MaibornWolff/clean-air/hardware/all_wood/pictures/frontview_open_side.png

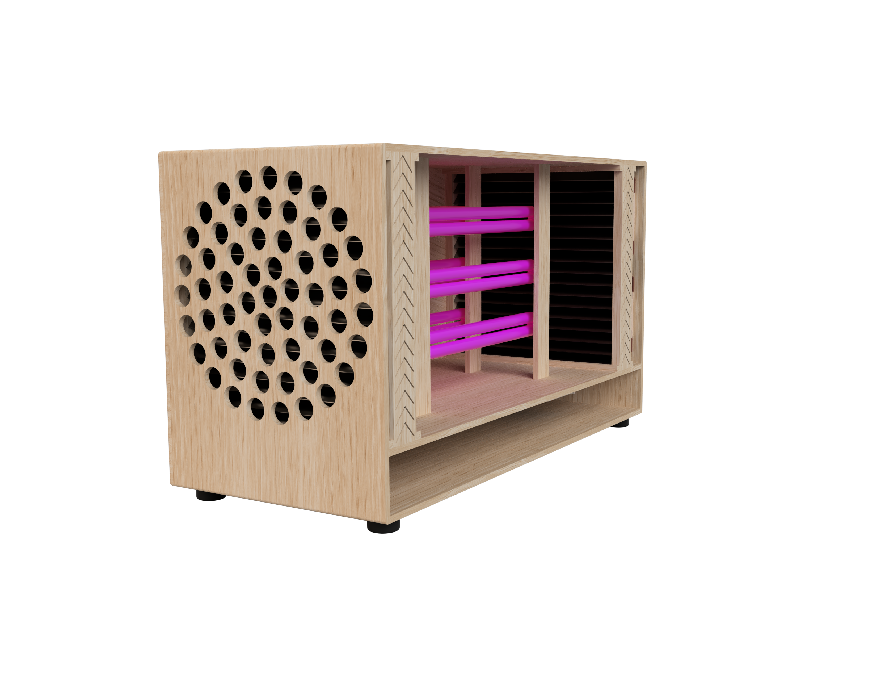
hardware/all_wood/pictures/frontview_open_side.png
