MaibornWolff/clean-air/hardware/common/uv_back_holder.stl

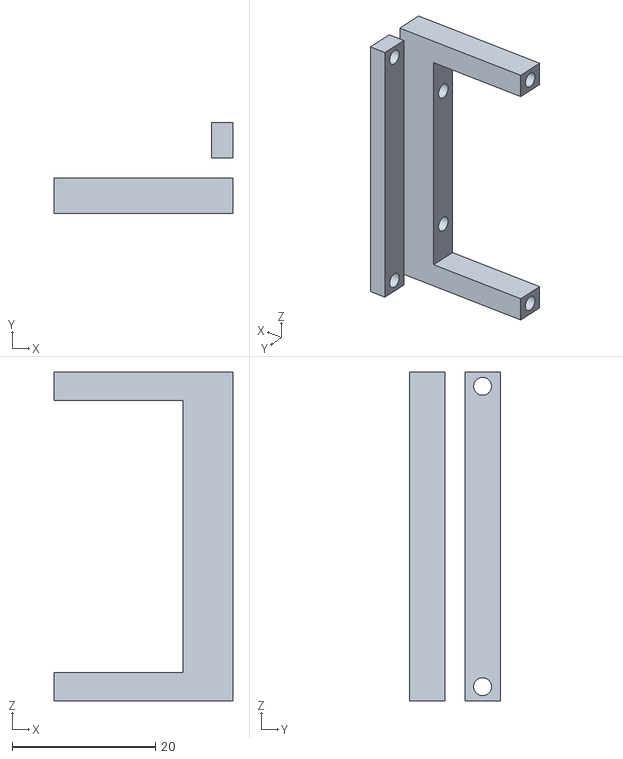
[picture p28: CAD file, 2020-12-15]
hardware/common/uv_back_holder.stl
25.0 x 12.8 x 46.0
