MaibornWolff/clean-air/hardware/all_3dprinted/universalBoxPlate_io.stl

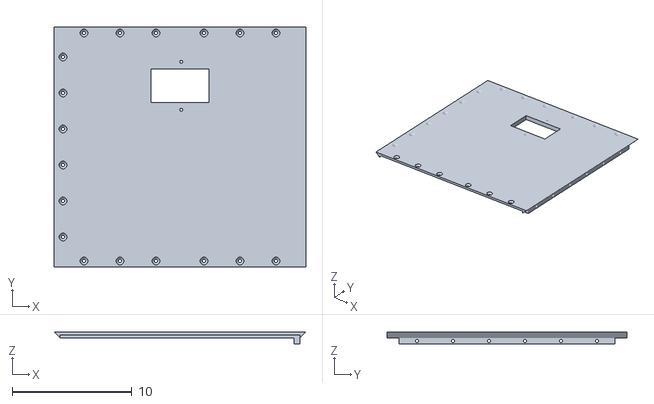
[picture p29: CAD file, 2020-11-02]
hardware/all_3dprinted/universalBoxPlate_io.stl
21.0 x 20.0 x 1.00
