MaibornWolff/clean-air/hardware/common/honeycombfront_lowprofile_fan.stl

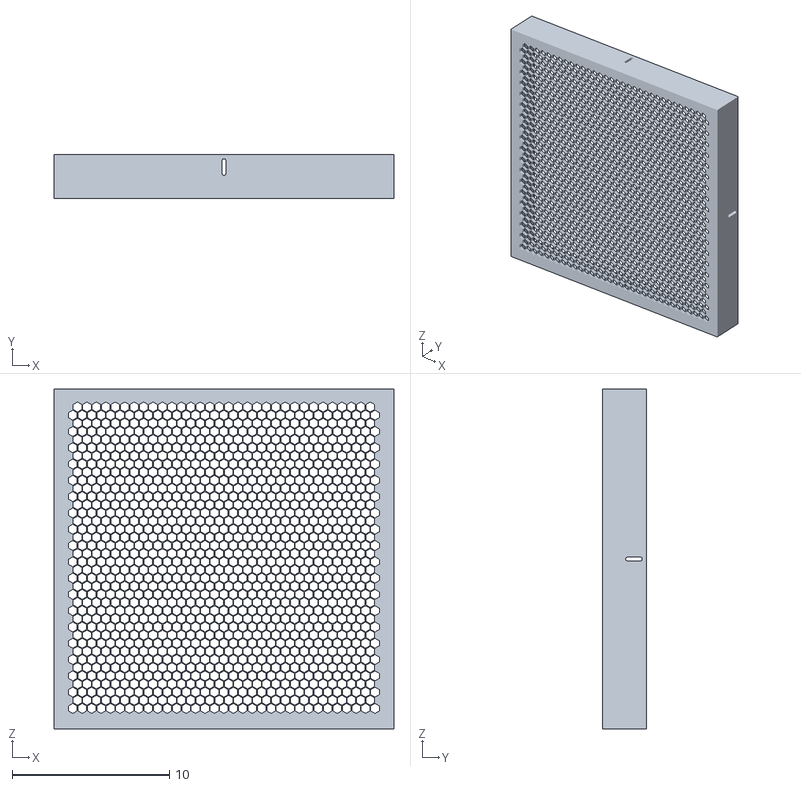
[picture p30: CAD file, 2020-11-02]
hardware/common/honeycombfront_lowprofile_fan.stl
21.6 x 2.80 x 21.6
