MaibornWolff/clean-air/documentation/images/3d_printable/inside_unfinished_1.jpg

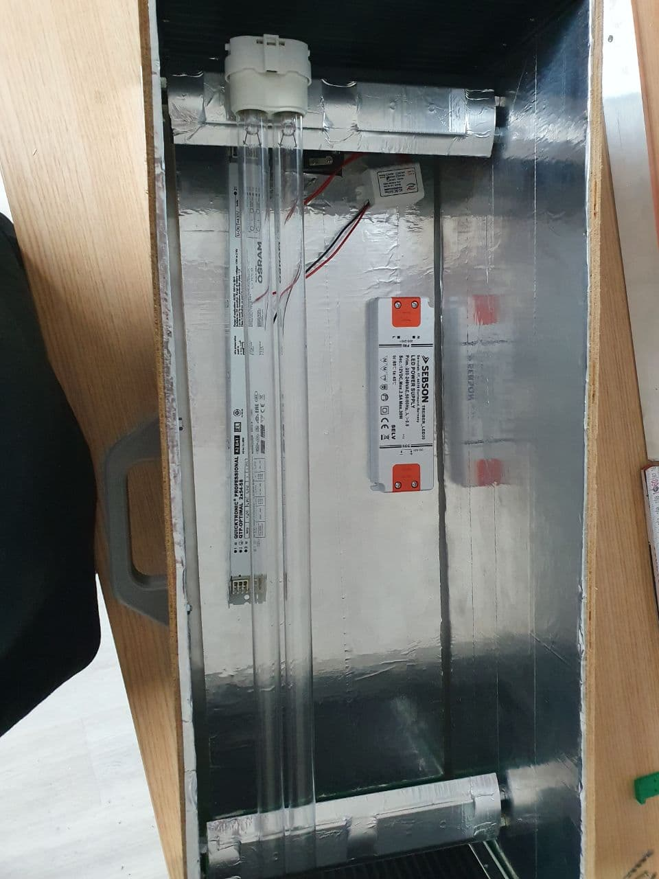
documentation/images/3d_printable/inside_unfinished_1.jpg
