MaibornWolff/clean-air/documentation/images/3d_printable/io_to_cut.jpg

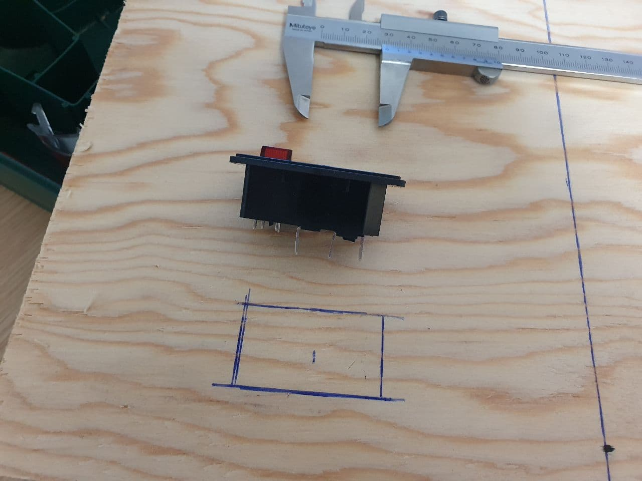
documentation/images/3d_printable/io_to_cut.jpg
