MaibornWolff/clean-air/documentation/images/3d_printable/messy_elektronics.jpg

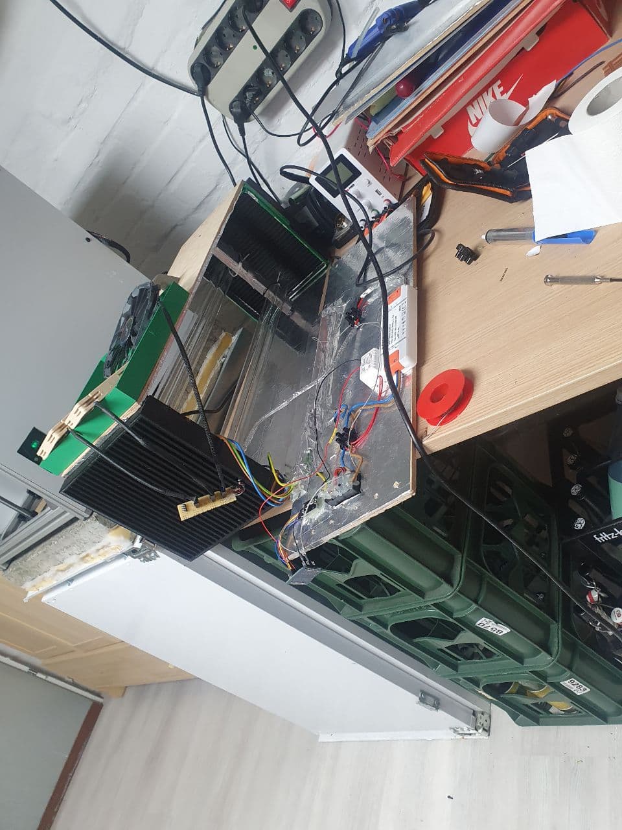
documentation/images/3d_printable/messy_elektronics.jpg
