MaibornWolff/clean-air/documentation/images/3d_printable/schable_sample.jpg

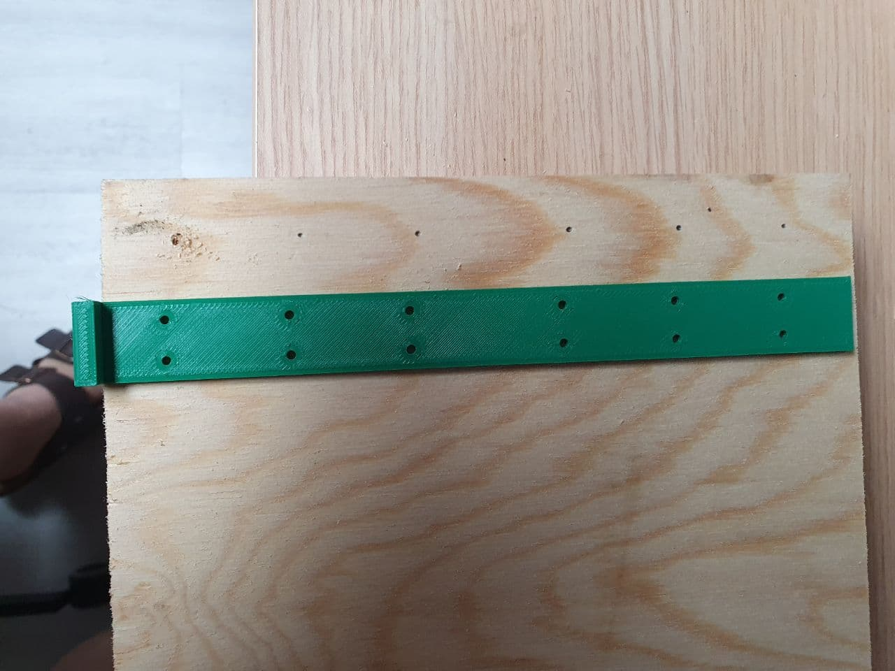
documentation/images/3d_printable/schable_sample.jpg
