MaibornWolff/clean-air/documentation/images/3d_printable/side_view.jpg

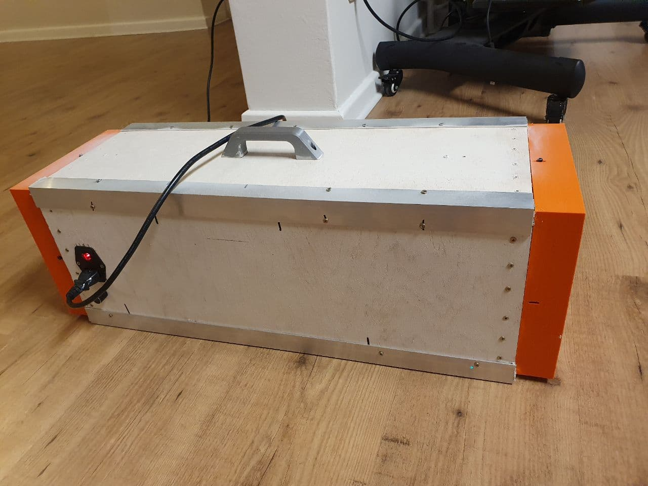
documentation/images/3d_printable/side_view.jpg
