MaibornWolff/clean-air/documentation/images/3d_printable/side_with_knob.jpg

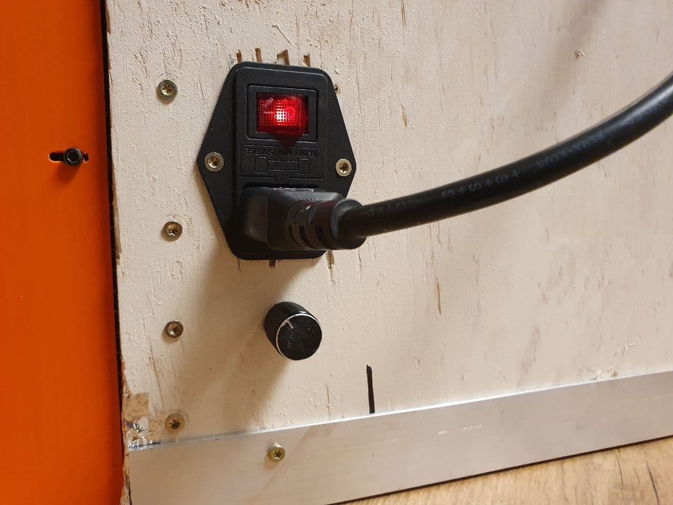
documentation/images/3d_printable/side_with_knob.jpg
