MaibornWolff/clean-air/documentation/images/3d_printable/uvc_holder_hole.jpg

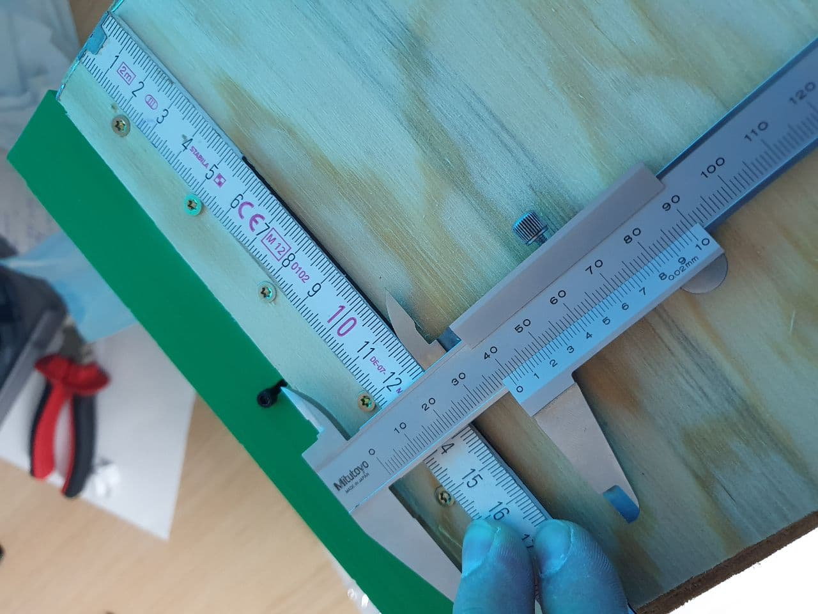
documentation/images/3d_printable/uvc_holder_hole.jpg
