MaibornWolff/clean-air/documentation/images/3d_printable/uvc_holder_wrapped.jpg

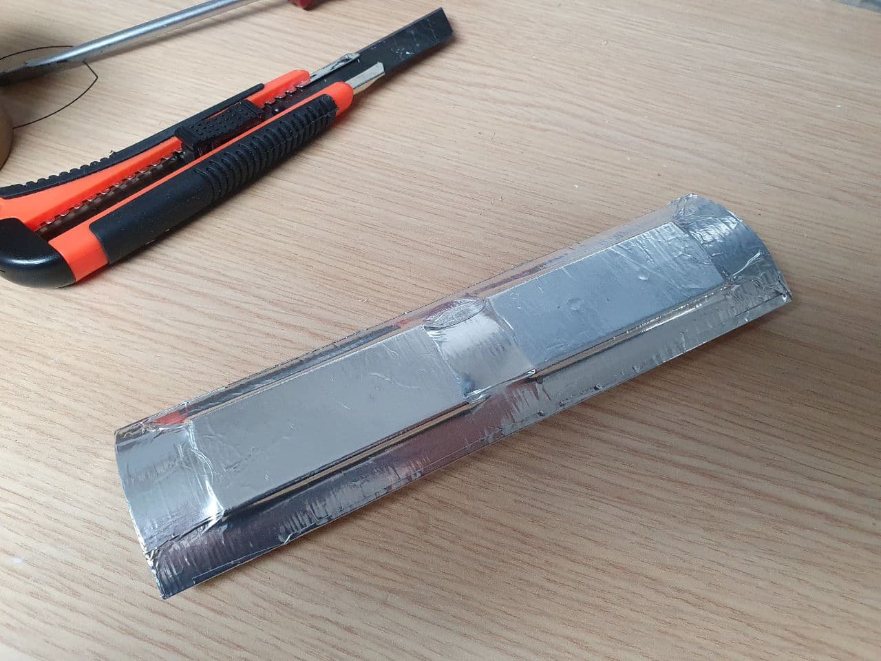
documentation/images/3d_printable/uvc_holder_wrapped.jpg
