MaibornWolff/clean-air/firmware/include/defaults.h

#ifndef DEFAULTS_H_
#define DEFAULTS_H_

// Serial Console Speed
const unsigned long BAUD_RATE = 115200;

// Logging
#define TAG "cleanair"

// default SSID for AP
#define AP_SSID "CleanAirDevice"

#endif
